nikoschalikias/scaleRap/docs/IMG_20160905_202137.jpg

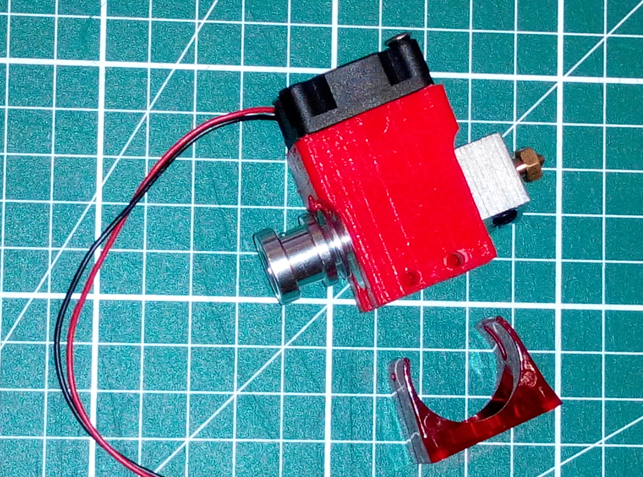
docs/IMG_20160905_202137.jpg
