nikoschalikias/scaleRap/docs/nixal_reprap4040_e3dsecureFan30mm_9.JPG

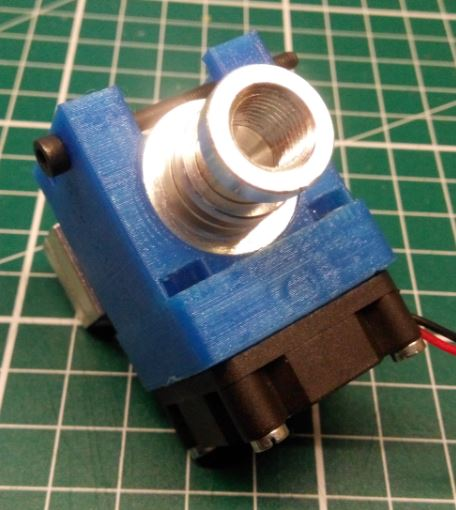
docs/nixal_reprap4040_e3dsecureFan30mm_9.JPG
