nikoschalikias/scaleRap/stl/nixal_reprap4040_centrifugalFanDuctVolcano.stl

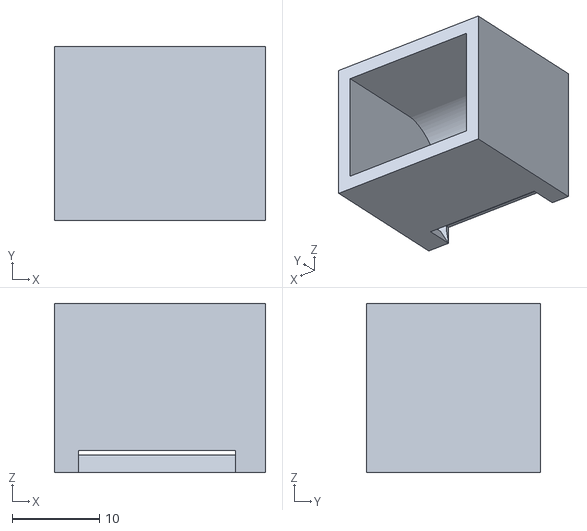
[picture p30: CAD file, 2016-10-19]
stl/nixal_reprap4040_centrifugalFanDuctVolcano.stl
24.2 x 20.0 x 19.4
