nikoschalikias/scaleRap/stl/nixal_reprap4040_gregWadesGears_Large44.stl

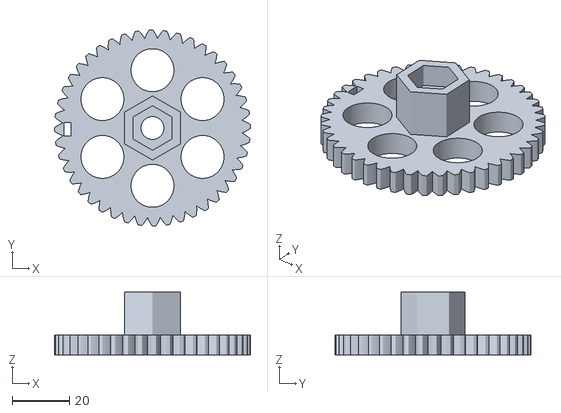
[picture p31: CAD file, 2016-10-17]
stl/nixal_reprap4040_gregWadesGears_Large44.stl
68.5 x 68.5 x 22.0
