nikoschalikias/scaleRap/stl/nixal_reprap4040_centrifugalFanDuct.stl

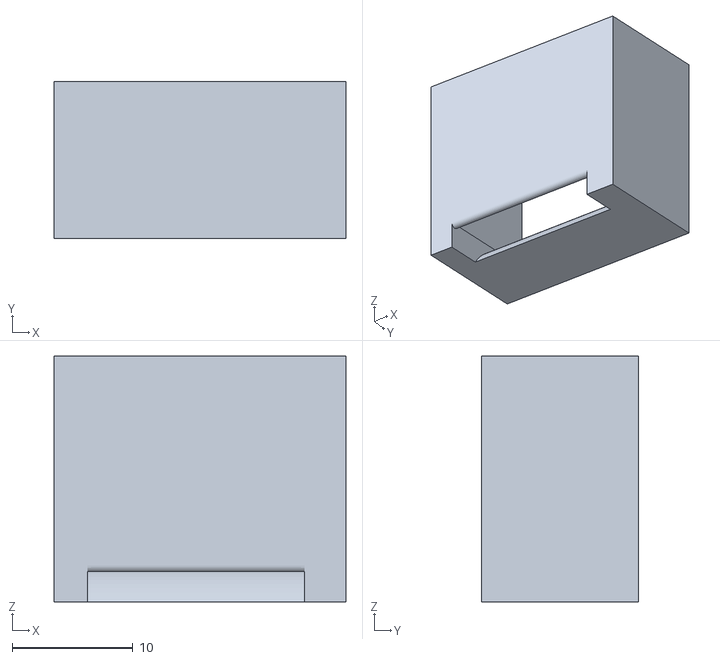
[picture p32: CAD file, 2016-10-17]
stl/nixal_reprap4040_centrifugalFanDuct.stl
24.2 x 13.0 x 20.4
