nikoschalikias/scaleRap/stl/nixal_reprap4040_e3dSecureFan30mm.stl

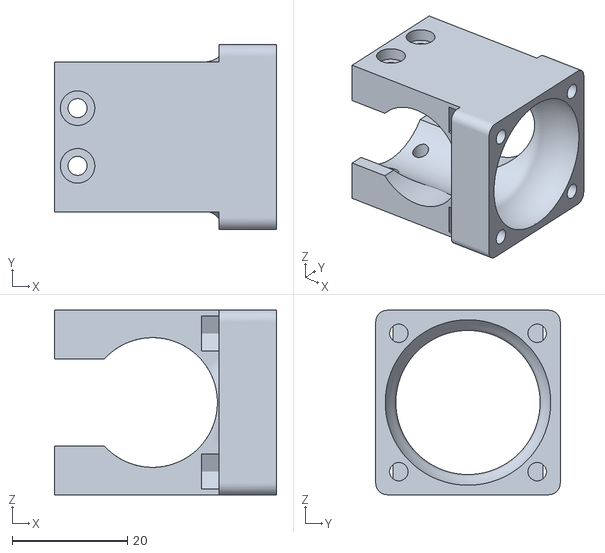
[picture p33: CAD file, 2016-10-16]
stl/nixal_reprap4040_e3dSecureFan30mm.stl
38.5 x 32.0 x 32.0
