nikoschalikias/scaleRap/stl/gregWadesGears_Large.stl

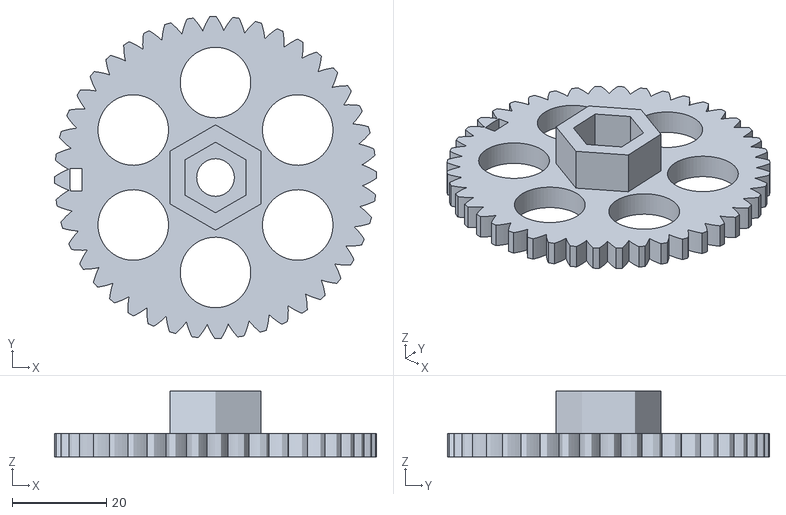
[picture p34: CAD file, 2016-10-16]
stl/gregWadesGears_Large.stl
68.5 x 68.5 x 14.0
