nikoschalikias/scaleRap/stl/fanBracket.stl

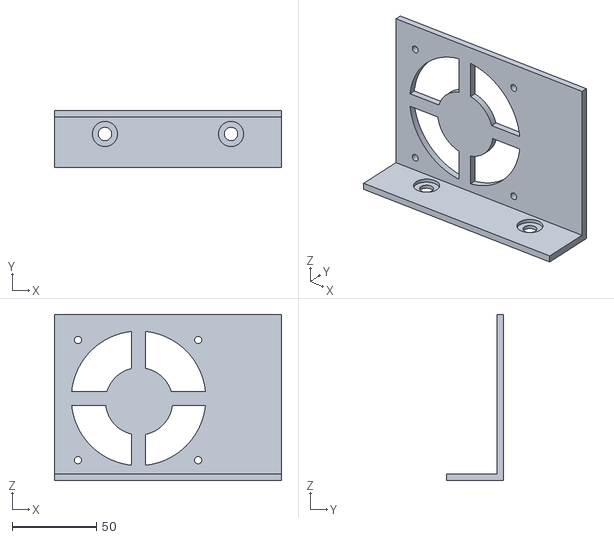
[picture p35: CAD file, 2016-10-09]
stl/fanBracket.stl
135.0 x 34.0 x 99.0
