nikoschalikias/scaleRap/stl/nixal_reprap4040_Ymotor.stl

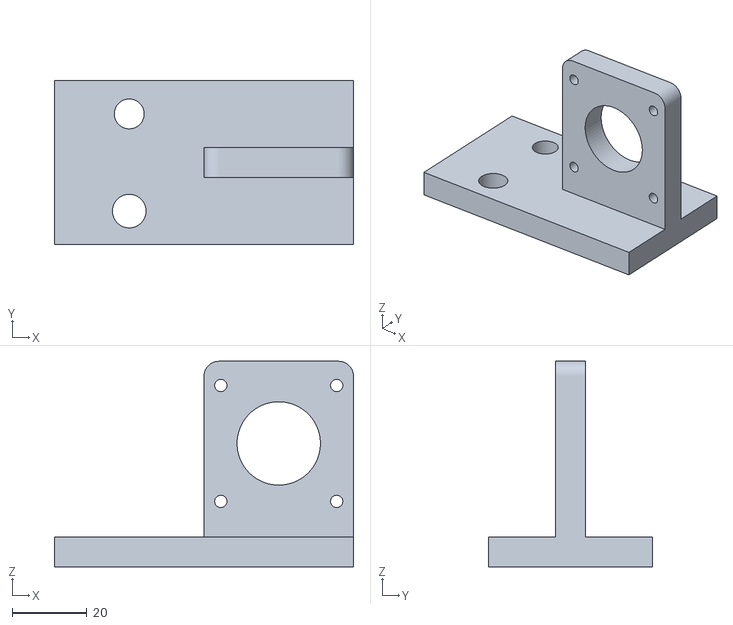
[picture p36: CAD file, 2016-09-28]
stl/nixal_reprap4040_Ymotor.stl
80.0 x 44.0 x 55.0
