nikoschalikias/scaleRap/stl/nixal_reprap4040_inductiveMount.stl

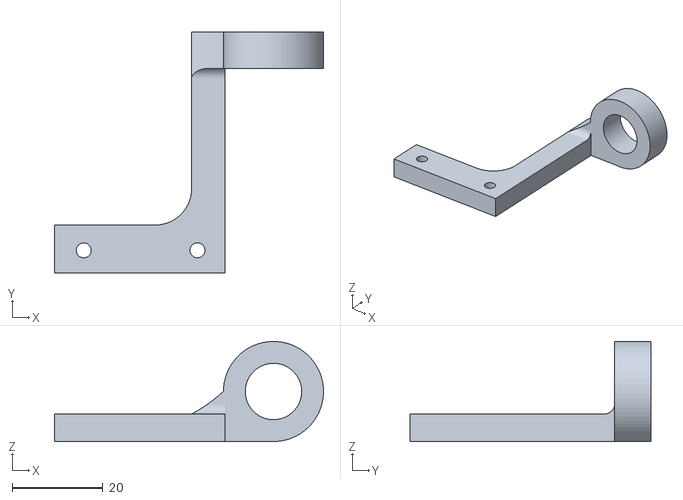
[picture p37: CAD file, 2016-09-28]
stl/nixal_reprap4040_inductiveMount.stl
59.1 x 53.0 x 22.0
