nikoschalikias/scaleRap/stl/nixal_reprap4040_endStop4040.stl

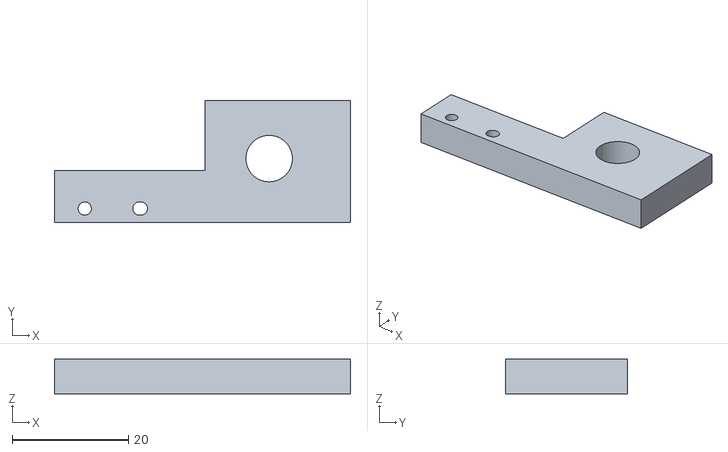
[picture p38: CAD file, 2016-09-28]
stl/nixal_reprap4040_endStop4040.stl
51.0 x 21.0 x 6.00
