nikoschalikias/scaleRap/stl/nixal_reprap_4040_cableHoldNema17.stl

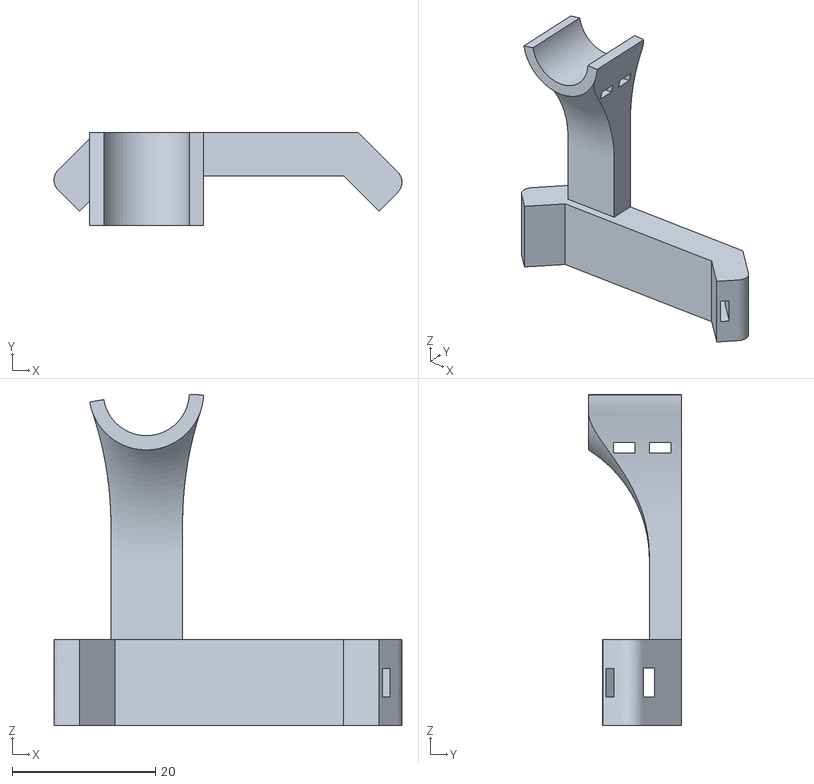
[picture p39: CAD file, 2016-09-28]
stl/nixal_reprap_4040_cableHoldNema17.stl
48.5 x 13.0 x 46.2
