nikoschalikias/scaleRap/stl/nixal_reprap4040_Yidler_part1.stl

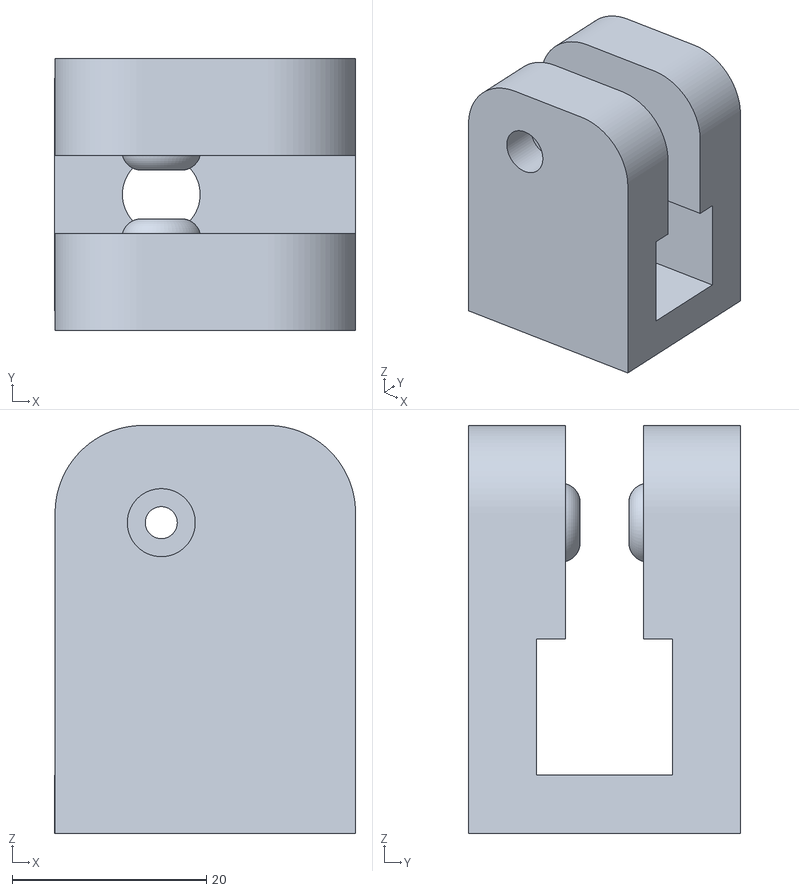
[picture p40: CAD file, 2016-09-28]
stl/nixal_reprap4040_Yidler_part1.stl
31.0 x 28.0 x 42.0
