nikoschalikias/scaleRap/stl/nixal_reprap_Ybracket.stl

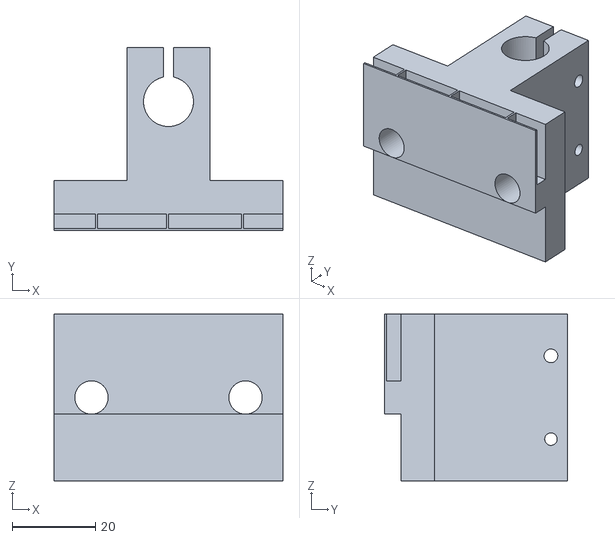
[picture p41: CAD file, 2016-09-28]
stl/nixal_reprap_Ybracket.stl
55.0 x 44.0 x 40.0
