nikoschalikias/scaleRap/stl/nixal_reprap4040_Yidler_part2.stl

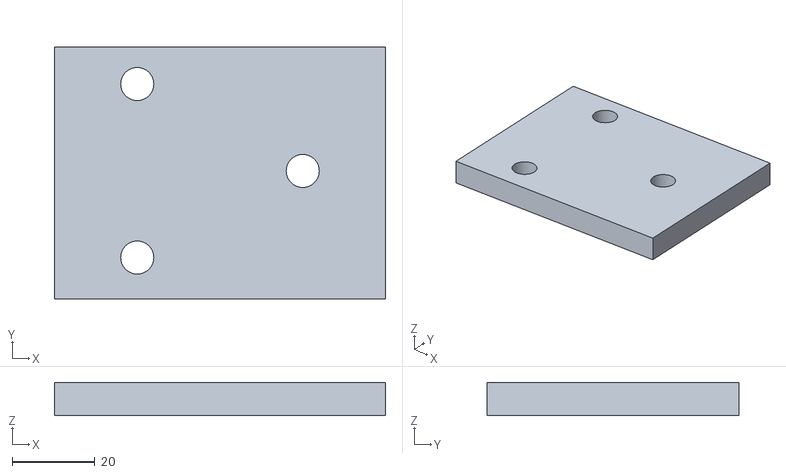
[picture p42: CAD file, 2016-09-28]
stl/nixal_reprap4040_Yidler_part2.stl
80.0 x 61.0 x 8.00
