nikoschalikias/scaleRap/stl/nixal_reprap4040_Yidler.stl

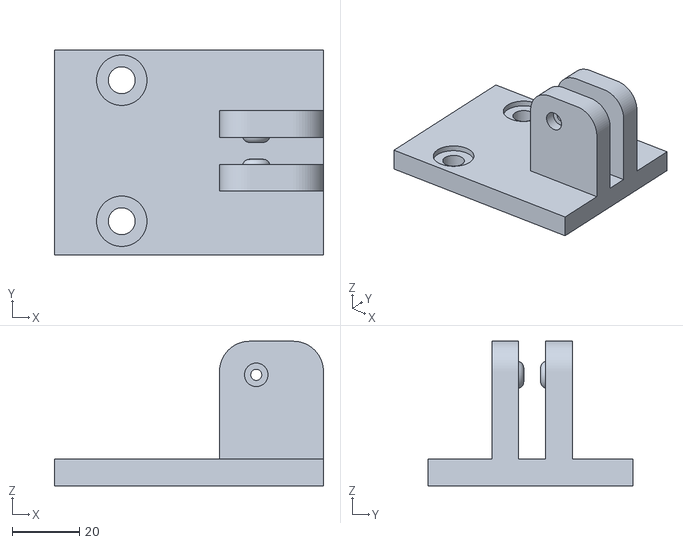
[picture p43: CAD file, 2016-09-15]
stl/nixal_reprap4040_Yidler.stl
80.0 x 61.0 x 43.0
