nikoschalikias/scaleRap/stl/nixal_rerap_Xmotor.stl

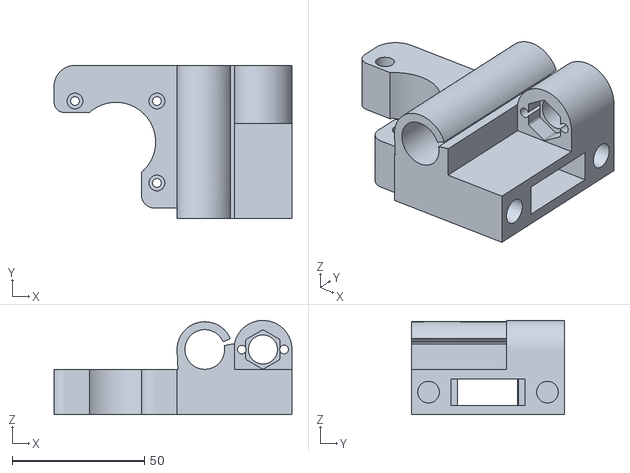
[picture p44: CAD file, 2016-09-05]
stl/nixal_rerap_Xmotor.stl
90.0 x 58.0 x 35.6
