nikoschalikias/scaleRap/stl/nixal_reprap_ZbracketCompatible_non4040.stl

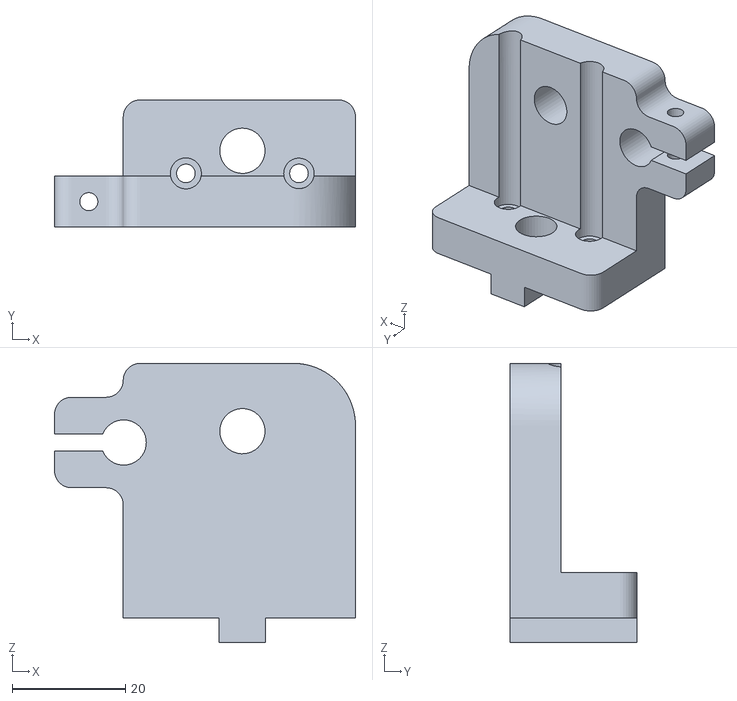
[picture p45: CAD file, 2016-09-05]
stl/nixal_reprap_ZbracketCompatible_non4040.stl
53.2 x 22.5 x 49.4
