nikoschalikias/scaleRap/stl/nixal_reprap_4040_endStop.stl

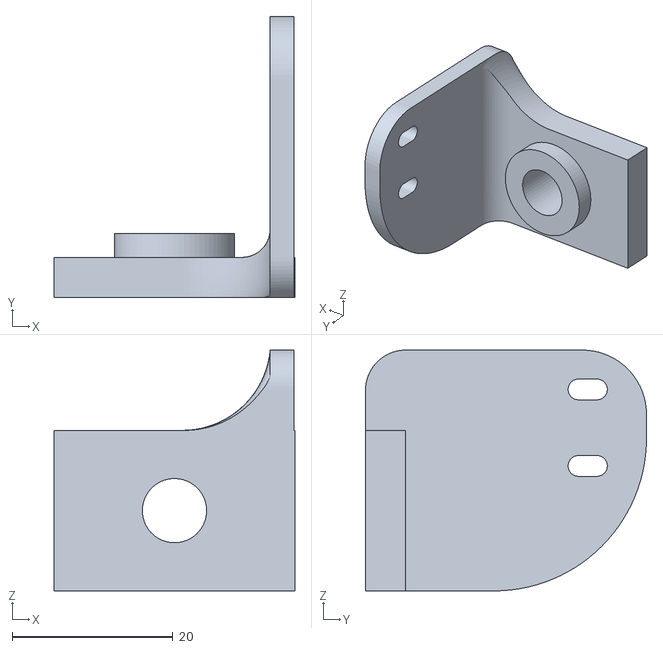
[picture p46: CAD file, 2016-09-05]
stl/nixal_reprap_4040_endStop.stl
30.0 x 35.0 x 30.0
