nikoschalikias/scaleRap/stl/nixal_reprap_ZbracketCompatible_8mm.stl

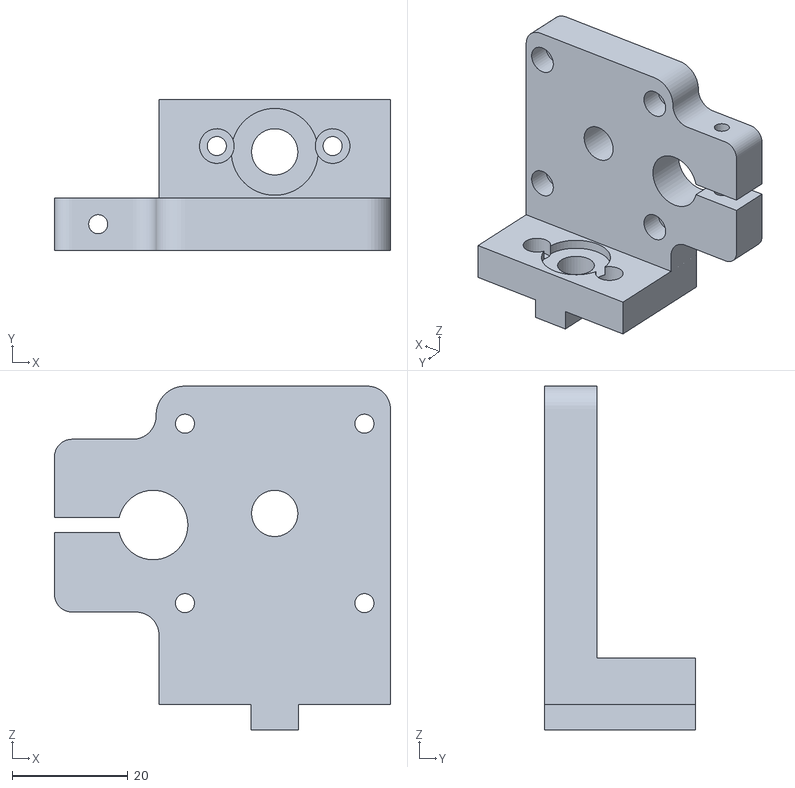
[picture p47: CAD file, 2016-09-05]
stl/nixal_reprap_ZbracketCompatible_8mm.stl
58.0 x 26.0 x 59.4
