nikoschalikias/scaleRap/stl/nixal_reprap4040_spoolHolderBearing.stl

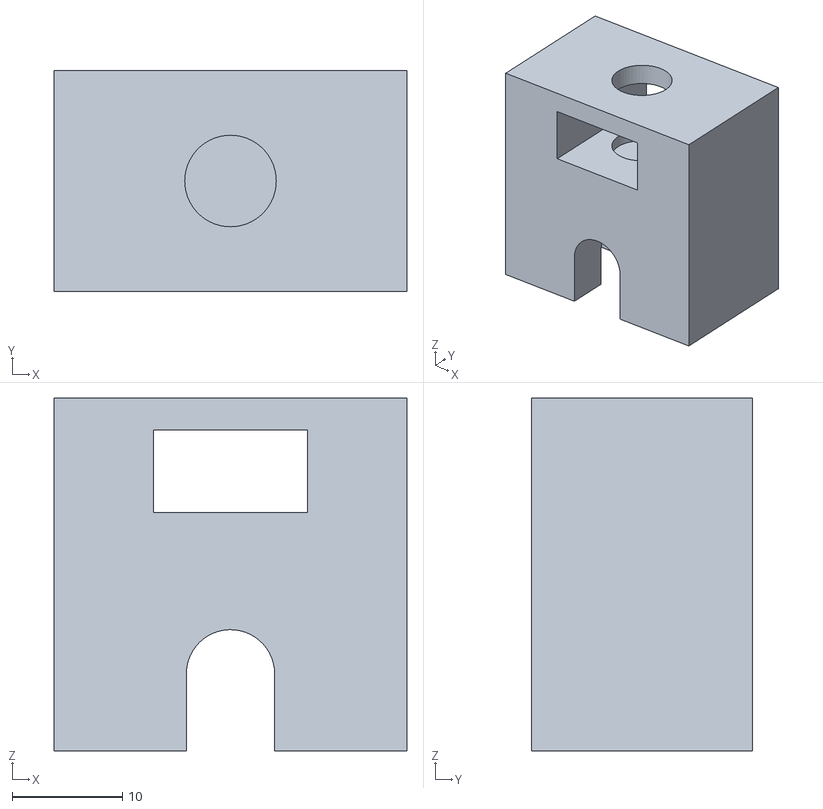
[picture p48: CAD file, 2016-09-05]
stl/nixal_reprap4040_spoolHolderBearing.stl
32.0 x 20.0 x 32.0
