nikoschalikias/scaleRap/stl/nixal_reprap_Xcariage.stl

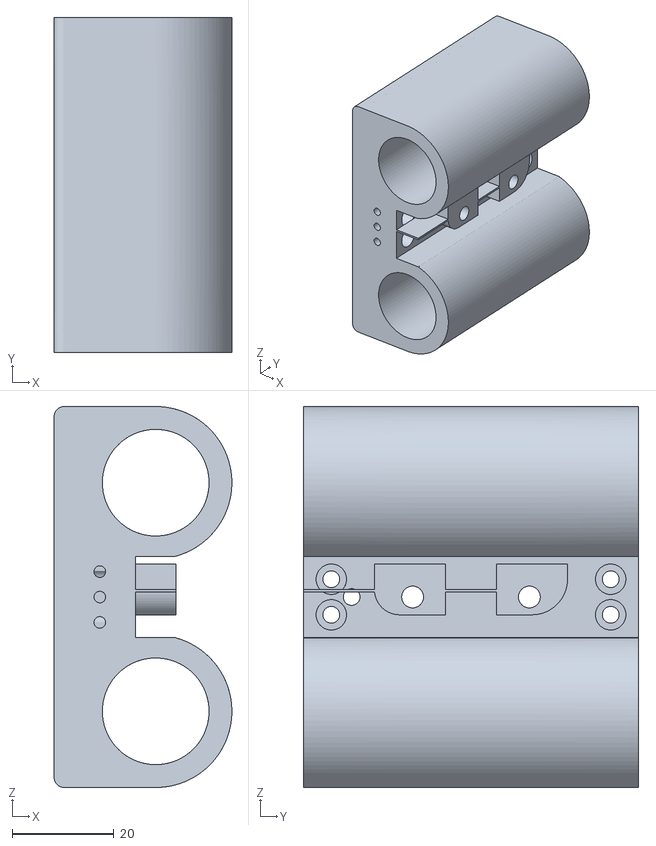
[picture p49: CAD file, 2016-09-05]
stl/nixal_reprap_Xcariage.stl
35.0 x 66.0 x 75.0
