nikoschalikias/scaleRap/stl/item4040_leg.stl

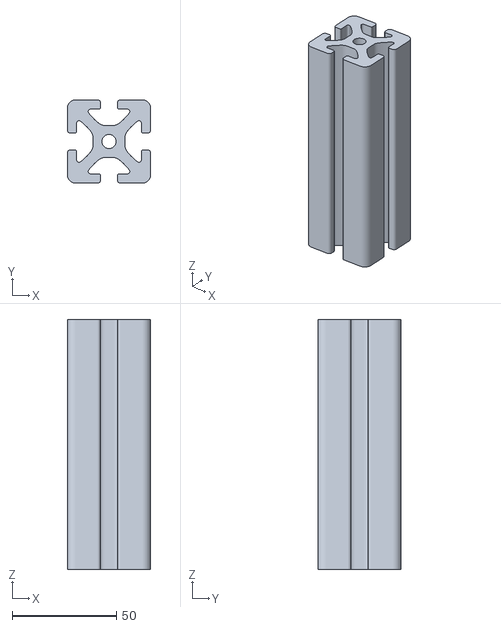
[picture p50: CAD file, 2016-09-05]
stl/item4040_leg.stl
40.0 x 40.0 x 120.0
