nikoschalikias/scaleRap/stl/nixal_reprap4040_Xtensioner.stl

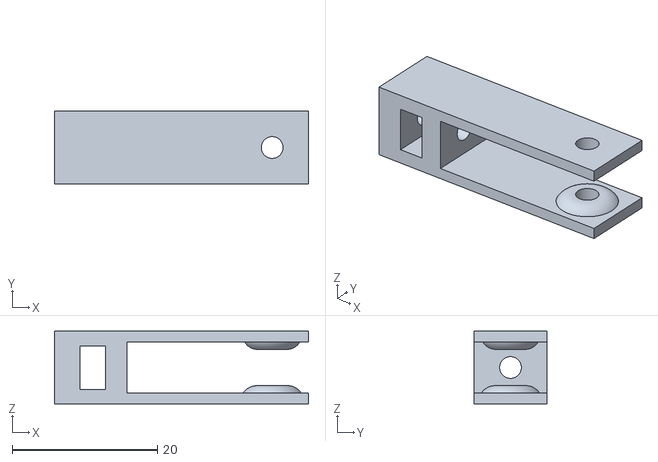
[picture p51: CAD file, 2016-09-05]
stl/nixal_reprap4040_Xtensioner.stl
35.0 x 10.0 x 10.0
