nikoschalikias/scaleRap/stl/shaftY.stl

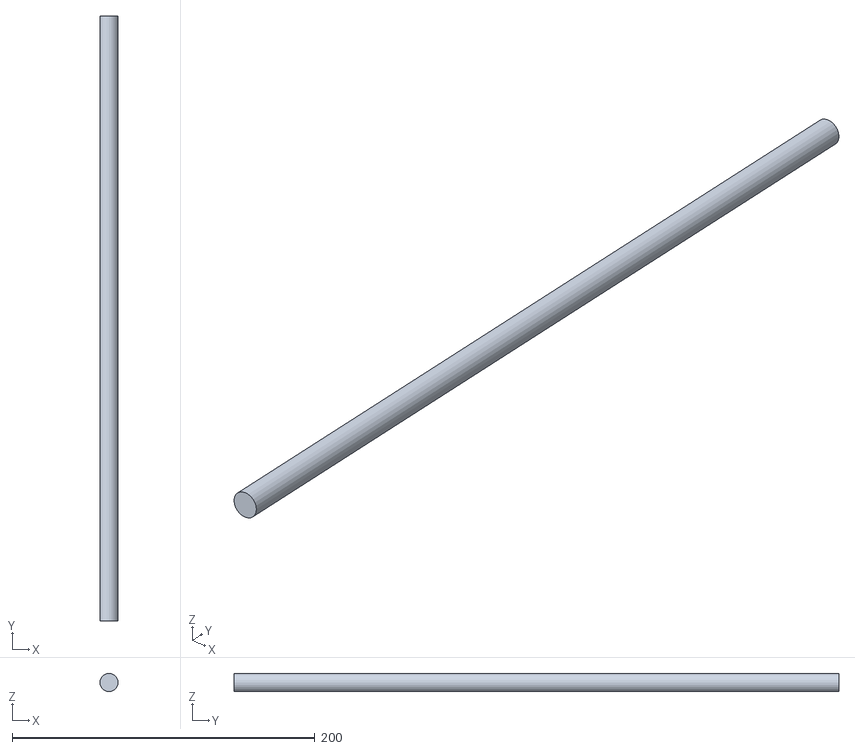
[picture p52: CAD file, 2016-09-05]
stl/shaftY.stl
12.0 x 400.0 x 12.0
