nikoschalikias/scaleRap/stl/nixal_reprap_4040_cableClip1.stl

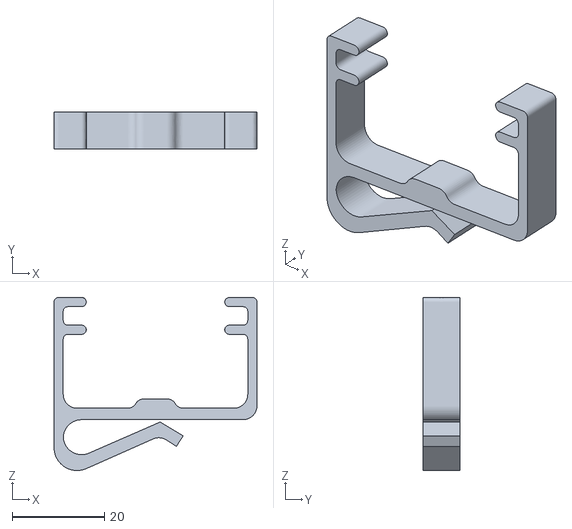
[picture p53: CAD file, 2016-09-05]
stl/nixal_reprap_4040_cableClip1.stl
44.0 x 8.00 x 37.5
