nikoschalikias/scaleRap/stl/nixal_reprap4040_XtensionerHolder.stl

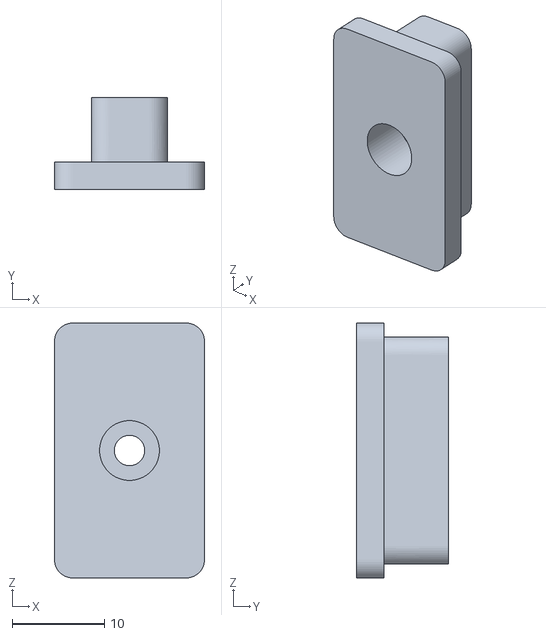
[picture p54: CAD file, 2016-09-05]
stl/nixal_reprap4040_XtensionerHolder.stl
16.3 x 10.0 x 27.7
