nikoschalikias/scaleRap/stl/nixal_reprap4040_ZendStop.stl

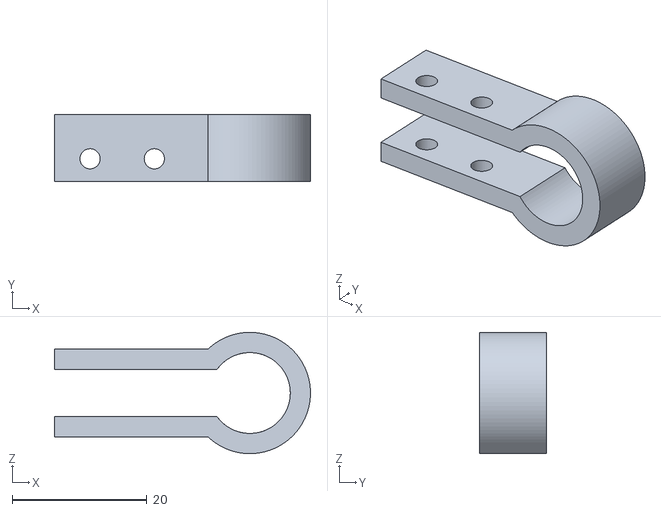
[picture p55: CAD file, 2016-09-05]
stl/nixal_reprap4040_ZendStop.stl
38.0 x 10.0 x 18.0
