nikoschalikias/scaleRap/stl/nuxal_reprap4040_Zadjust.stl

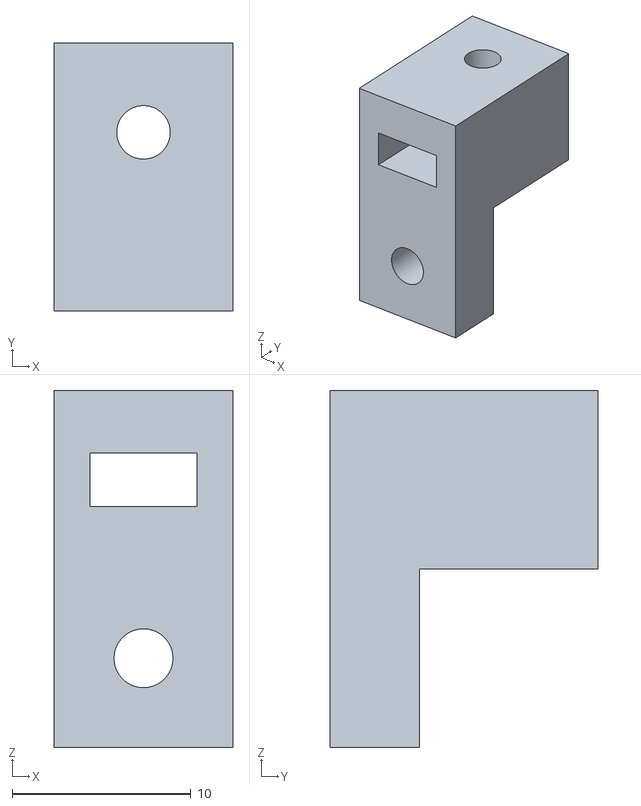
[picture p56: CAD file, 2016-09-05]
stl/nuxal_reprap4040_Zadjust.stl
10.0 x 15.0 x 20.0
