nikoschalikias/scaleRap/stl/item_4040.stl

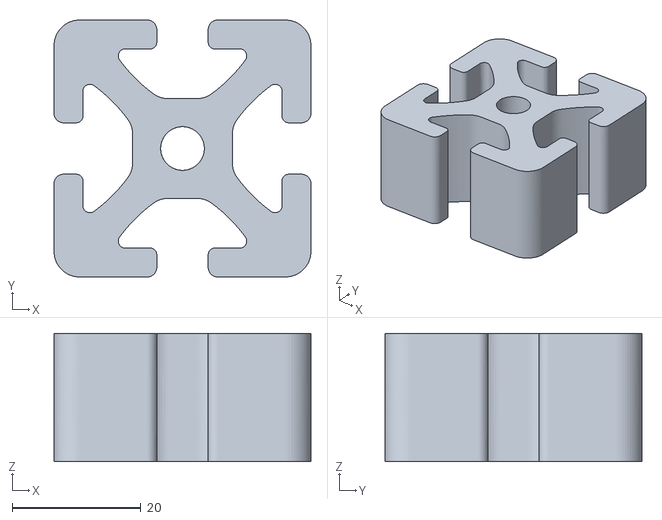
[picture p57: CAD file, 2016-09-05]
stl/item_4040.stl
40.0 x 40.0 x 20.0
