nikoschalikias/scaleRap/stl/nixal_reprap4040_nBlocks.stl

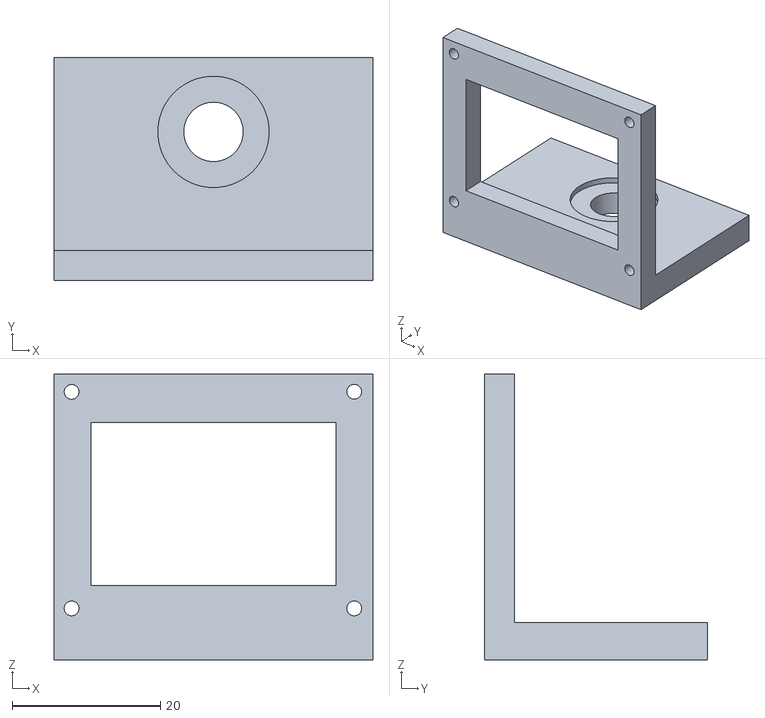
[picture p58: CAD file, 2016-09-05]
stl/nixal_reprap4040_nBlocks.stl
43.0 x 30.0 x 38.5
