nikoschalikias/scaleRap/stl/nixal_spoolHolder38.stl

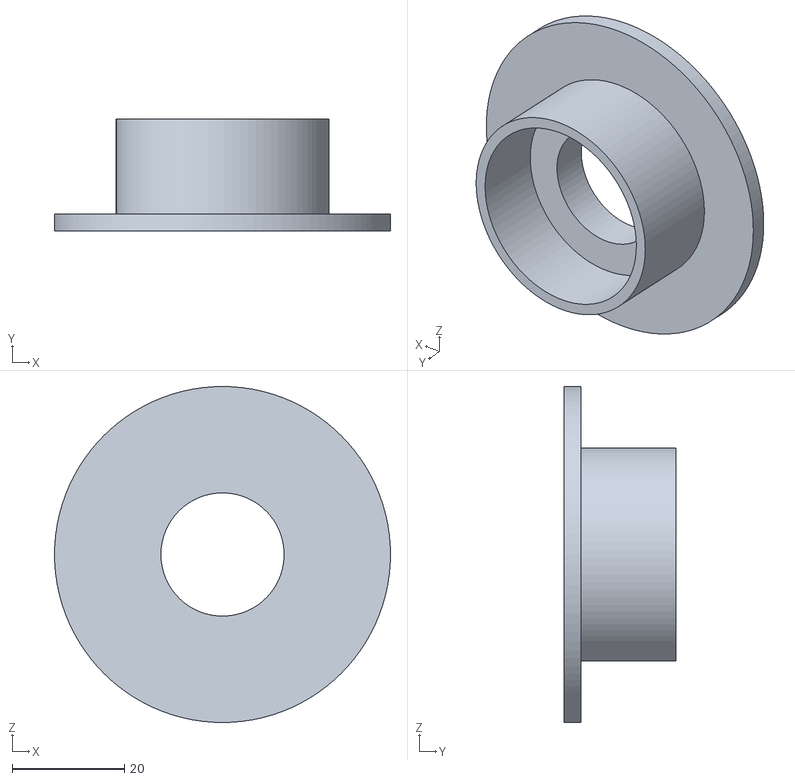
[picture p59: CAD file, 2016-09-05]
stl/nixal_spoolHolder38.stl
60.0 x 20.0 x 60.0
