nikoschalikias/scaleRap/stl/thing_415923-ALNOA.stl

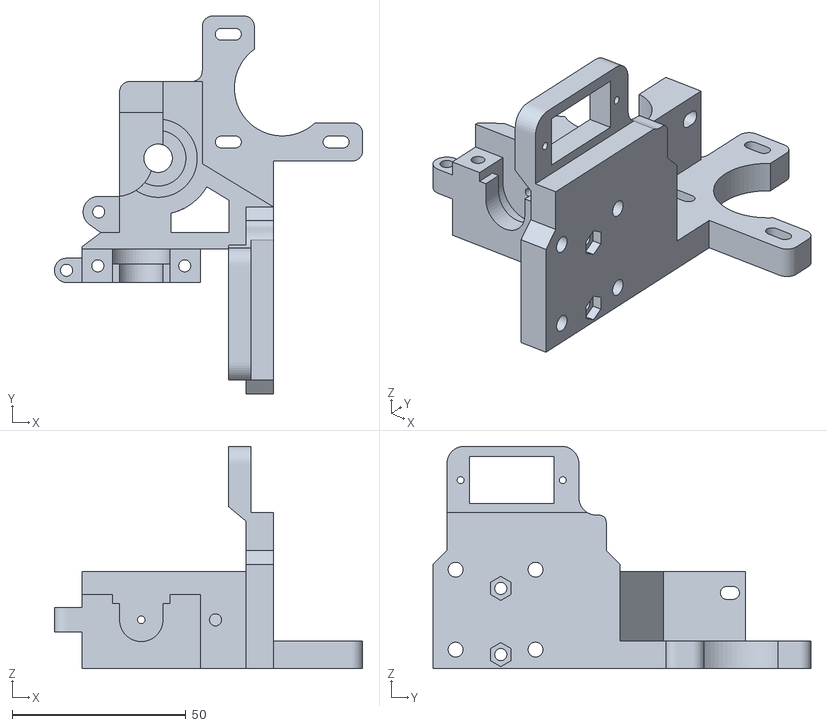
[picture p60: CAD file, 2016-09-05]
stl/thing_415923-ALNOA.stl
88.7 x 108.7 x 64.0
