nikoschalikias/scaleRap/stl/nixal_reprap_XZ_Compatible_robust_idler_PRINT_MIRRORED.stl

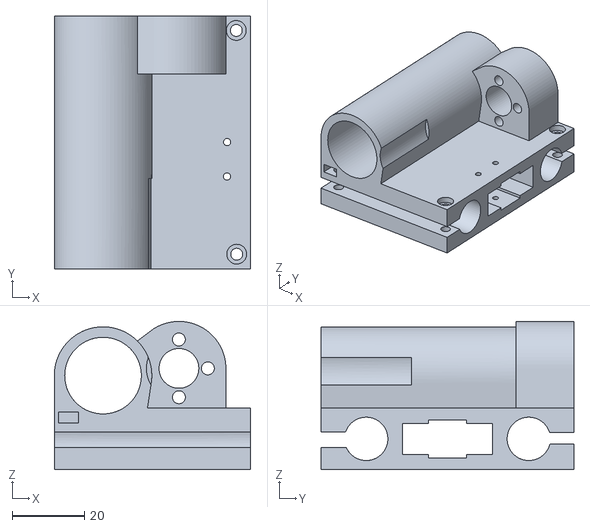
[picture p61: CAD file, 2016-09-05]
stl/nixal_reprap_XZ_Compatible_robust_idler_PRINT_MIRRORED.stl
54.4 x 70.0 x 41.0
