nikoschalikias/scaleRap/stl/nixal_reprap4040_psuClamp1.stl

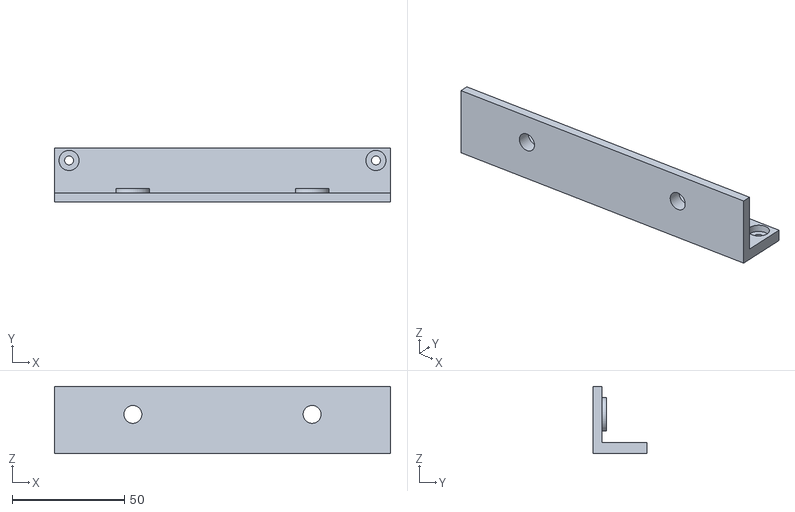
[picture p62: CAD file, 2016-09-05]
stl/nixal_reprap4040_psuClamp1.stl
150.0 x 24.0 x 30.0
