nikoschalikias/scaleRap/stl/nixal_reprap_XmotorCompatible.stl

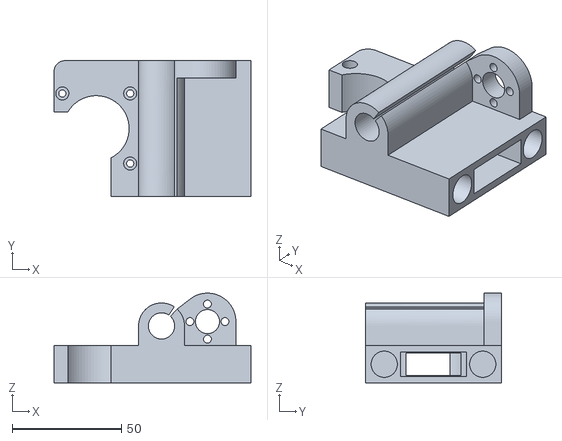
[picture p63: CAD file, 2016-09-05]
stl/nixal_reprap_XmotorCompatible.stl
90.0 x 62.0 x 41.0
