nikoschalikias/scaleRap/stl/nixal_reprap4040_Ybearing.stl

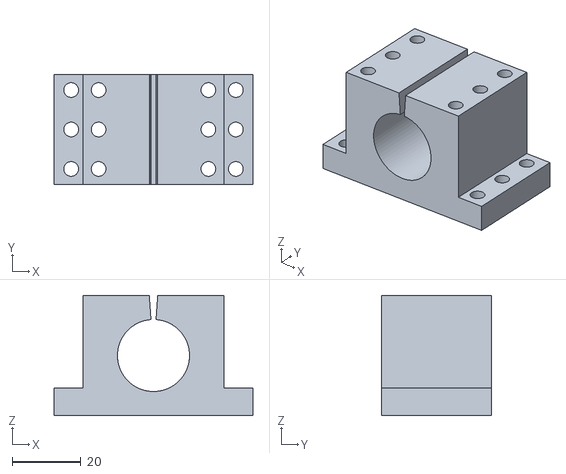
[picture p64: CAD file, 2016-09-05]
stl/nixal_reprap4040_Ybearing.stl
58.0 x 32.0 x 35.0
