nikoschalikias/scaleRap/stl/nixal_reprap_XZ_Compatible_robust.stl

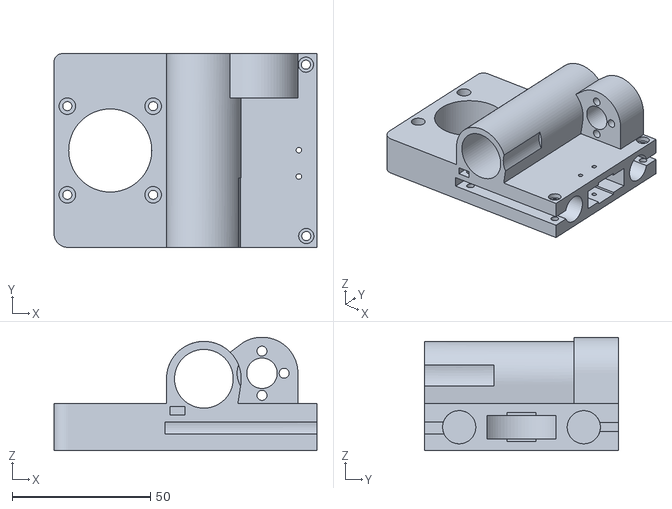
[picture p65: CAD file, 2016-09-05]
stl/nixal_reprap_XZ_Compatible_robust.stl
95.0 x 70.0 x 41.0
