nikoschalikias/scaleRap/stl/nixal_reprap_Zbracket.stl

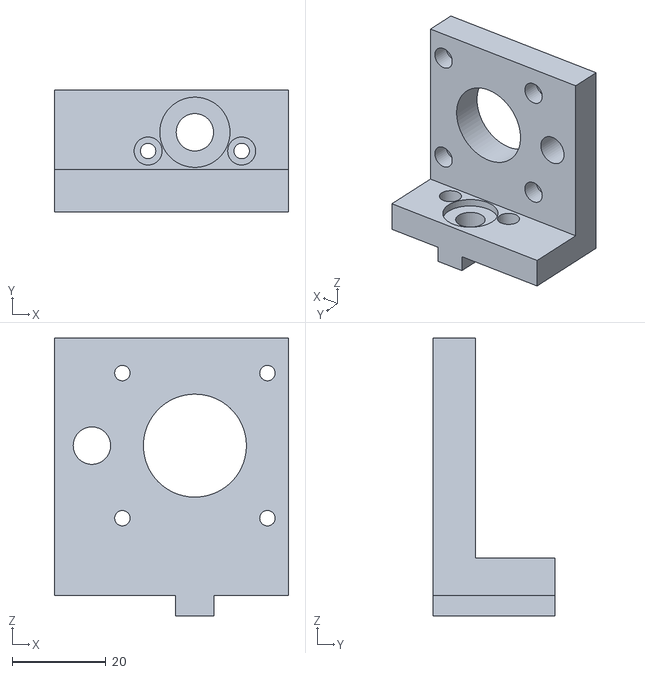
[picture p66: CAD file, 2016-09-05]
stl/nixal_reprap_Zbracket.stl
50.0 x 26.0 x 59.4
