nikoschalikias/scaleRap/stl/nixal_tnutM8_itmSlot8.stl

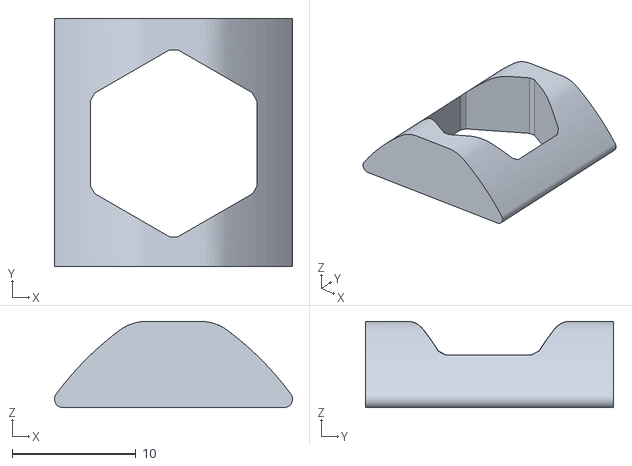
[picture p67: CAD file, 2016-09-05]
stl/nixal_tnutM8_itmSlot8.stl
19.2 x 20.0 x 6.95
