nikoschalikias/scaleRap/stl/nixal_reprap4040_GregWadesReloaded_cap.stl

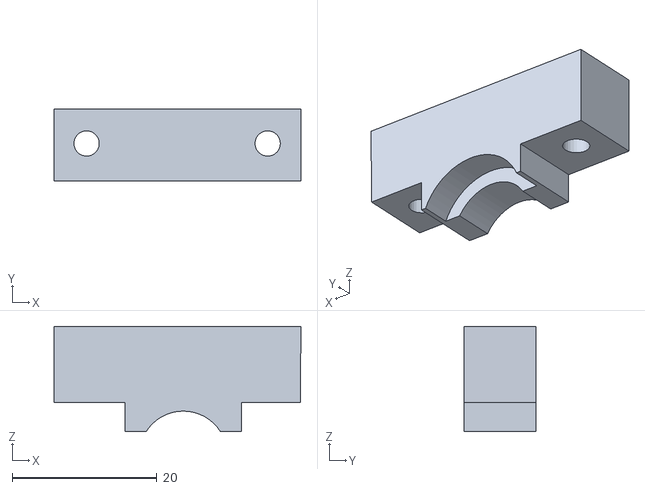
[picture p68: CAD file, 2016-09-05]
stl/nixal_reprap4040_GregWadesReloaded_cap.stl
34.1 x 10.00 x 14.5
