nikoschalikias/scaleRap/stl/item4040_side.stl

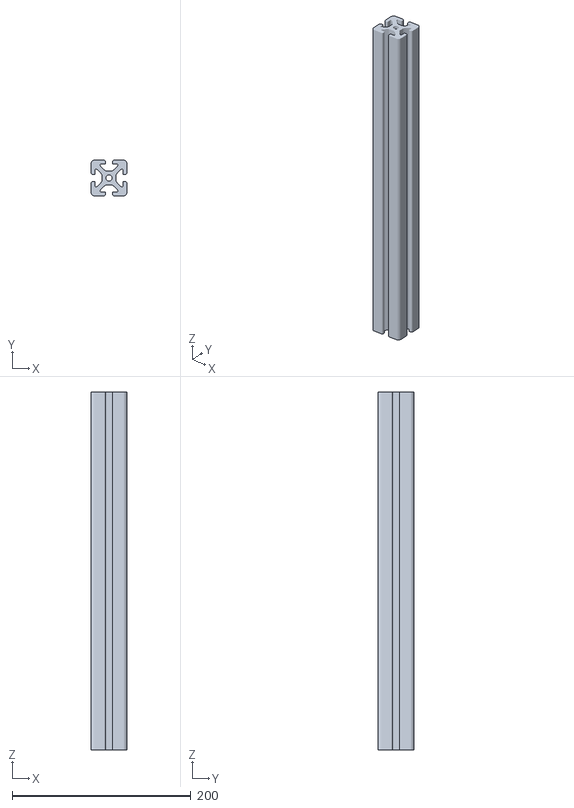
[picture p69: CAD file, 2016-09-05]
stl/item4040_side.stl
40.0 x 40.0 x 400.0
