nikoschalikias/scaleRap/stl/nixal_prusaI3_spoolHolderClear.stl

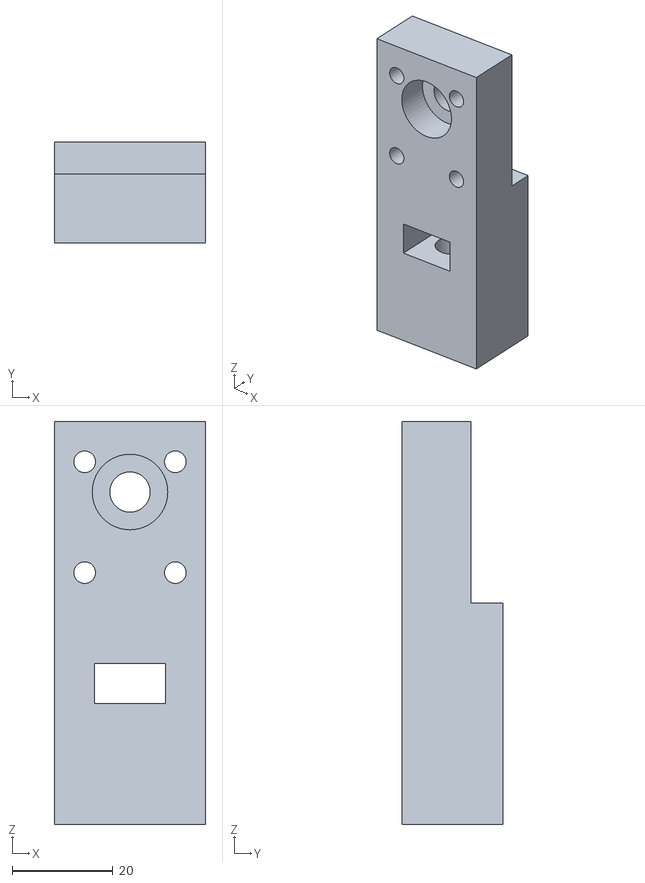
[picture p70: CAD file, 2016-09-05]
stl/nixal_prusaI3_spoolHolderClear.stl
30.0 x 20.0 x 80.0
