nikoschalikias/scaleRap/stl/nixal_reprap4040_GregWadesReloaded.stl

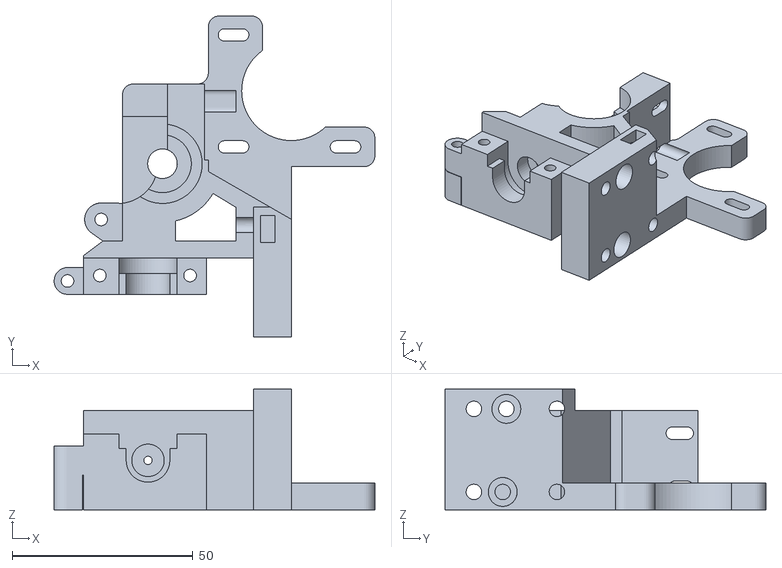
[picture p71: CAD file, 2016-09-05]
stl/nixal_reprap4040_GregWadesReloaded.stl
88.8 x 88.9 x 33.5
