nikoschalikias/scaleRap/stl/nixal_tnutM8_itmSlot8_55.stl

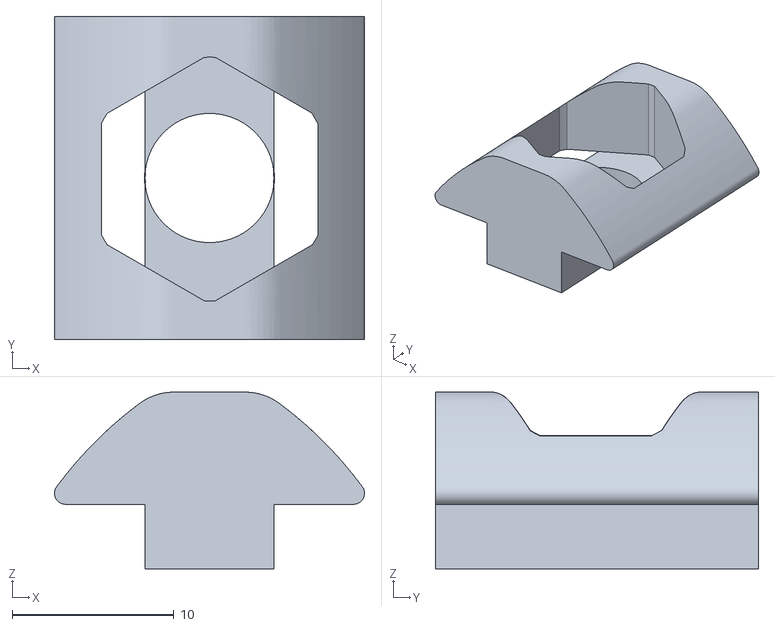
[picture p72: CAD file, 2016-09-05]
stl/nixal_tnutM8_itmSlot8_55.stl
19.2 x 20.0 x 10.9
