nikoschalikias/scaleRap/stl/nixal_reprap4040_rampsBracket.stl

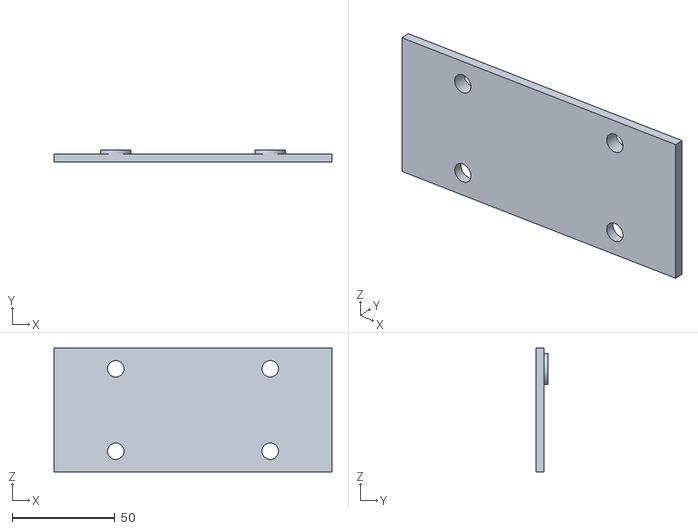
[picture p73: CAD file, 2016-09-05]
stl/nixal_reprap4040_rampsBracket.stl
135.0 x 6.00 x 60.0
