nikoschalikias/scaleRap/stl/nixal_reprap_4040_Ramps.stl

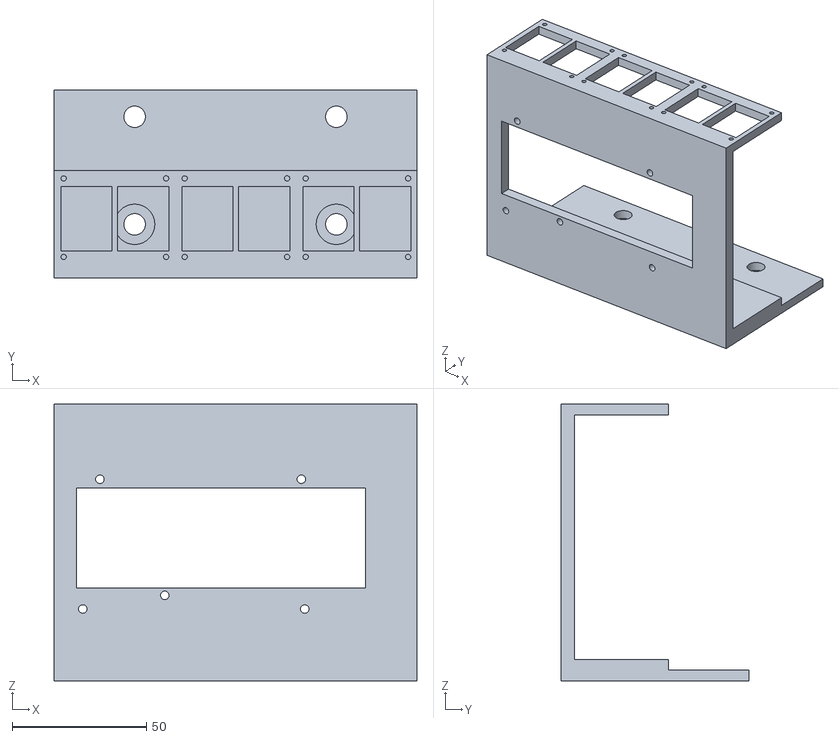
[picture p74: CAD file, 2016-09-05]
stl/nixal_reprap_4040_Ramps.stl
135.0 x 70.0 x 103.0
