nikoschalikias/scaleRap/stl/nixal_reprap_XidlerCompatible.stl

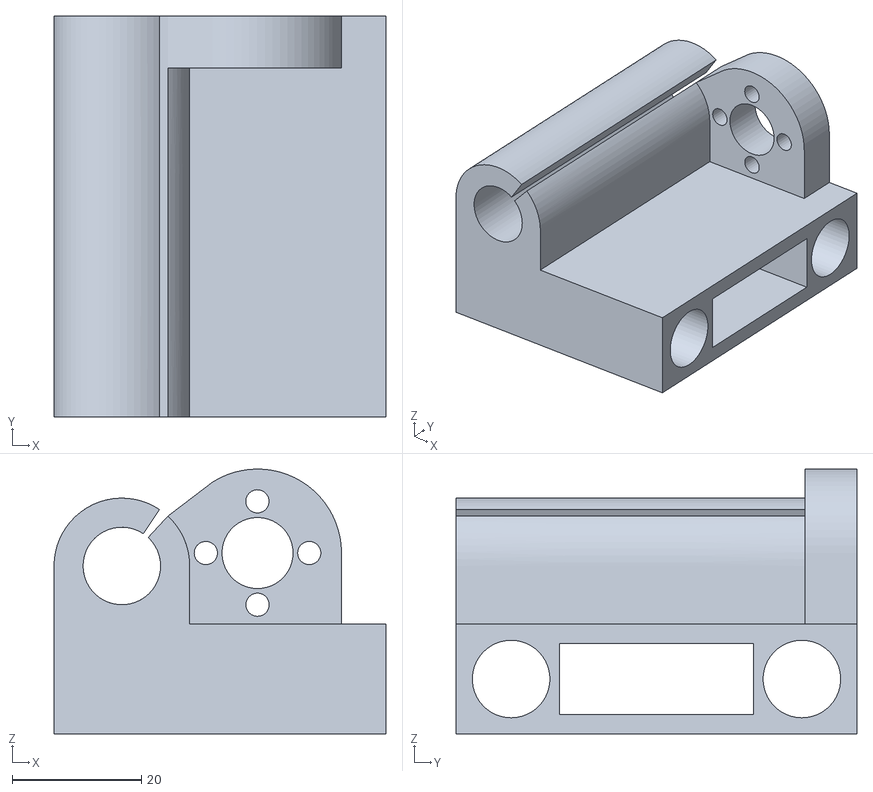
[picture p75: CAD file, 2016-09-05]
stl/nixal_reprap_XidlerCompatible.stl
51.4 x 62.0 x 41.0
